S-March/smarchWand_Public/Firmware/ble_app_barebone_wand/src/config/user_config.h

/**
 ****************************************************************************************
 *
 * @file user_config.h
 *
 * @brief User configuration file.
 *
 * Copyright (C) 2015-2020 Dialog Semiconductor.
 * This computer program includes Confidential, Proprietary Information
 * of Dialog Semiconductor. All Rights Reserved.
 *
 ****************************************************************************************
 */

#ifndef _USER_CONFIG_H_
#define _USER_CONFIG_H_

/*
 * INCLUDE FILES
 ****************************************************************************************
 */

#include "app_user_config.h"
#include "arch_api.h"
#include "app_default_handlers.h"
#include "app_adv_data.h"
#include "co_bt.h"

/*
 * DEFINES
 ****************************************************************************************
 */

/*
 ****************************************************************************************
 *
 * Privacy / Addressing configuration
 *
 ****************************************************************************************
 */

/*************************************************************************
 * Privacy Capabilities and address configuration of local device:
 * - APP_CFG_ADDR_PUB               No Privacy, Public BDA
 * - APP_CFG_ADDR_STATIC            No Privacy, Random Static BDA
 * - APP_CFG_HOST_PRIV_RPA          Host Privacy, RPA, Public Identity
 * - APP_CFG_HOST_PRIV_NRPA         Host Privacy, NRPA (non-connectable ONLY)
 * - APP_CFG_CNTL_PRIV_RPA_PUB      Controller Privacy, RPA or PUB, Public Identity
 * - APP_CFG_CNTL_PRIV_RPA_RAND     Controller Privacy, RPA, Public Identity
 *
 * Select only one option for privacy / addressing configuration.
 **************************************************************************
 */
#define USER_CFG_ADDRESS_MODE       APP_CFG_ADDR_PUB

/*************************************************************************
 * Controller Privacy Mode:
 * - APP_CFG_CNTL_PRIV_MODE_NETWORK Controler Privacy Network mode (default)
 * - APP_CFG_CNTL_PRIV_MODE_DEVICE  Controler Privacy Device mode
 *
 * Select only one option for controller privacy mode configuration.
 **************************************************************************
 */
#define USER_CFG_CNTL_PRIV_MODE     APP_CFG_CNTL_PRIV_MODE_NETWORK

/*
 * VARIABLES
 ****************************************************************************************
 */

/******************************************
 * Default sleep mode. Possible values are:
 *
 * - ARCH_SLEEP_OFF
 * - ARCH_EXT_SLEEP_ON
 * - ARCH_EXT_SLEEP_OTP_COPY_ON
 *
 ******************************************
 */
static const sleep_state_t app_default_sleep_mode = ARCH_SLEEP_OFF;

/*
 ****************************************************************************************
 *
 * Advertising configuration
 *
 ****************************************************************************************
 */
static const struct advertise_configuration user_adv_conf = {

    .addr_src = APP_CFG_ADDR_SRC(USER_CFG_ADDRESS_MODE),

    /// Minimum interval for advertising
    .intv_min = MS_TO_BLESLOTS(687.5),                    // 687.5ms

    /// Maximum interval for advertising
    .intv_max = MS_TO_BLESLOTS(687.5),                    // 687.5ms

    /**
     *  Advertising channels map:
     * - ADV_CHNL_37_EN:   Advertising channel map for channel 37.
     * - ADV_CHNL_38_EN:   Advertising channel map for channel 38.
     * - ADV_CHNL_39_EN:   Advertising channel map for channel 39.
     * - ADV_ALL_CHNLS_EN: Advertising channel map for channel 37, 38 and 39.
     */
    .channel_map = ADV_ALL_CHNLS_EN,

    /*************************
     * Advertising information
     *************************
     */

    /// Host information advertising data (GAPM_ADV_NON_CONN and GAPM_ADV_UNDIRECT)
    /// Advertising mode :
    /// - GAP_NON_DISCOVERABLE: Non discoverable mode
    /// - GAP_GEN_DISCOVERABLE: General discoverable mode
    /// - GAP_LIM_DISCOVERABLE: Limited discoverable mode
    /// - GAP_BROADCASTER_MODE: Broadcaster mode
    .mode = GAP_GEN_DISCOVERABLE,

    /// Host information advertising data (GAPM_ADV_NON_CONN and GAPM_ADV_UNDIRECT)
    /// Advertising filter policy:
    /// - ADV_ALLOW_SCAN_ANY_CON_ANY: Allow both scan and connection requests from anyone
    /// - ADV_ALLOW_SCAN_ANY_CON_WLST: Allow both scan req from anyone and connection req from
    ///                                White List devices only
    .adv_filt_policy = ADV_ALLOW_SCAN_ANY_CON_ANY,

    /// Address of peer device
    /// NOTE: Meant for directed advertising (ADV_DIRECT_IND)
    .peer_addr = {0x1, 0x2, 0x3, 0x4, 0x5, 0x6},

    /// Address type of peer device (0=public/1=random)
    /// NOTE: Meant for directed advertising (ADV_DIRECT_IND)
    .peer_addr_type = 0,
};

/*
 ****************************************************************************************
 *
 * Advertising or scan response data for the following cases:
 *
 * - ADV_IND: Connectable undirected advertising event.
 *    - The maximum length of the user defined advertising data shall be 28 bytes.
 *    - The Flags data type are written by the related ROM function, hence the user shall
 *      not include them in the advertising data. The related ROM function adds 3 bytes in
 *      the start of the advertising data that are to be transmitted over the air.
 *    - The maximum length of the user defined response data shall be 31 bytes.
 *
 * - ADV_NONCONN_IND: Non-connectable undirected advertising event.
 *    - The maximum length of the user defined advertising data shall be 31 bytes.
 *    - The Flags data type may be omitted, hence the user can use all the 31 bytes for
 *      data.
 *    - The scan response data shall be empty.
 *
 * - ADV_SCAN_IND: Scannable undirected advertising event.
 *    - The maximum length of the user defined advertising data shall be 31 bytes.
 *    - The Flags data type may be omitted, hence the user can use all the 31 bytes for
 *      data.
 *    - The maximum length of the user defined response data shall be 31 bytes.
 ****************************************************************************************
 */
/// Advertising data
#define USER_ADVERTISE_DATA         "\x03"\
                                    ADV_TYPE_COMPLETE_LIST_16BIT_SERVICE_IDS\
                                    ADV_UUID_DEVICE_INFORMATION_SERVICE

/// Advertising data length - maximum 28 bytes, 3 bytes are reserved to set
#define USER_ADVERTISE_DATA_LEN               (sizeof(USER_ADVERTISE_DATA)-1)

/// Scan response data
#define USER_ADVERTISE_SCAN_RESPONSE_DATA ""

/// Scan response data length- maximum 31 bytes
#define USER_ADVERTISE_SCAN_RESPONSE_DATA_LEN (sizeof(USER_ADVERTISE_SCAN_RESPONSE_DATA)-1)

/*
 ****************************************************************************************
 *
 * Device name.
 *
 * - If there is space left in the advertising or scan response data the device name is
 *   copied there. The device name can be anytime read by a connected peer, if the
 *   application supports it.
 * - The Bluetooth device name can be up to 248 bytes.
 *
 ****************************************************************************************
 */
/// Device name
#define USER_DEVICE_NAME        "smarchHouse"

/// Device name length
#define USER_DEVICE_NAME_LEN    (sizeof(USER_DEVICE_NAME)-1)

/*
 ****************************************************************************************
 *
 * GAPM configuration
 *
 ****************************************************************************************
 */
static const struct gapm_configuration user_gapm_conf = {
    /// Device Role: Central, Peripheral, Observer, Broadcaster or All roles. (@see enum gap_role)
    .role = GAP_ROLE_PERIPHERAL,

    /// Maximal MTU. Shall be set to 23 if Legacy Pairing is used, 65 if Secure Connection is used,
    /// more if required by the application
    .max_mtu = 23,

    /// Device Address Type
    .addr_type = APP_CFG_ADDR_TYPE(USER_CFG_ADDRESS_MODE),
    /// Duration before regenerating the Random Private Address when privacy is enabled
    .renew_dur = 15000,    // 15000 * 10ms = 150s is the minimum value

    /***********************
     * Privacy configuration
     ***********************
     */

    /// Random Static address
    // NOTE: The address shall comply with the following requirements:
    // - the two most significant bits of the address shall be equal to 1,
    // - all the remaining bits of the address shall NOT be equal to 1,
    // - all the remaining bits of the address shall NOT be equal to 0.
    // In case the {0x00, 0x00, 0x00, 0x00, 0x00, 0x00} null address is used, a
    // random static address will be automatically generated.
    .addr = {0x00, 0x00, 0x00, 0x00, 0x00, 0x00},

    /// Device IRK used for Resolvable Private Address generation (LSB first)
    .irk = {0x00, 0x01, 0x02, 0x03, 0x04, 0x05, 0x06, 0x07, 0x08, 0x09, 0x0a, 0x0b, 0x0c, 0x0d, 0x0e, 0x0f},

    /****************************
     * ATT database configuration
     ****************************
     */

    /// Attribute database configuration (@see enum gapm_att_cfg_flag)
    ///    7     6    5     4     3    2    1    0
    /// +-----+-----+----+-----+-----+----+----+----+
    /// | DBG | RFU | SC | PCP | APP_PERM |NAME_PERM|
    /// +-----+-----+----+-----+-----+----+----+----+
    /// - Bit [0-1]: Device Name write permission requirements for peer device (@see device_name_write_perm)
    /// - Bit [2-3]: Device Appearance write permission requirements for peer device (@see device_appearance_write_perm)
    /// - Bit [4]  : Slave Preferred Connection Parameters present
    /// - Bit [5]  : Service change feature present in GATT attribute database.
    /// - Bit [6]  : Reserved
    /// - Bit [7]  : Enable Debug Mode
    .att_cfg = GAPM_MASK_ATT_SVC_CHG_EN,

    /// GAP service start handle
    .gap_start_hdl = 0,

    /// GATT service start handle
    .gatt_start_hdl = 0,

    /**************************************************
     * Data packet length extension configuration (4.2)
     **************************************************
     */

    /// Maximal MPS
    .max_mps = 0,

    /// Maximal Tx octets (connInitialMaxTxOctets value, as defined in 4.2 Specification)
    .max_txoctets = 251,

    /// Maximal Tx time (connInitialMaxTxTime value, as defined in 4.2 Specification)
    .max_txtime = 2120,
};

/*
 ****************************************************************************************
 *
 * Parameter update configuration
 *
 ****************************************************************************************
 */
static const struct connection_param_configuration user_connection_param_conf = {
    /// Connection interval minimum measured in ble double slots (1.25ms)
    /// use the macro MS_TO_DOUBLESLOTS to convert from milliseconds (ms) to double slots
    .intv_min = MS_TO_DOUBLESLOTS(10),

    /// Connection interval maximum measured in ble double slots (1.25ms)
    /// use the macro MS_TO_DOUBLESLOTS to convert from milliseconds (ms) to double slots
    .intv_max = MS_TO_DOUBLESLOTS(20),

    /// Latency measured in connection events
    .latency = 0,

    /// Supervision timeout measured in timer units (10 ms)
    /// use the macro MS_TO_TIMERUNITS to convert from milliseconds (ms) to timer units
    .time_out = MS_TO_TIMERUNITS(1250),

    /// Minimum Connection Event Duration measured in ble double slots (1.25ms)
    /// use the macro MS_TO_DOUBLESLOTS to convert from milliseconds (ms) to double slots
    .ce_len_min = MS_TO_DOUBLESLOTS(0),

    /// Maximum Connection Event Duration measured in ble double slots (1.25ms)
    /// use the macro MS_TO_DOUBLESLOTS to convert from milliseconds (ms) to double slots
    .ce_len_max = MS_TO_DOUBLESLOTS(0),
};

/*
 ****************************************************************************************
 *
 * Default handlers configuration (applies only for @app_default_handlers.c)
 *
 ****************************************************************************************
 */
static const struct default_handlers_configuration  user_default_hnd_conf = {
    // Configure the advertise operation used by the default handlers
    // Possible values:
    //  - DEF_ADV_FOREVER
    //  - DEF_ADV_WITH_TIMEOUT
    .adv_scenario = DEF_ADV_FOREVER,

    // Configure the advertise period in case of DEF_ADV_WITH_TIMEOUT.
    // It is measured in timer units (3 min). Use MS_TO_TIMERUNITS macro to convert
    // from milliseconds (ms) to timer units.
    .advertise_period = MS_TO_TIMERUNITS(180000),

    // Configure the security start operation of the default handlers
    // if the security is enabled (CFG_APP_SECURITY)
    // Possible values:
    //  - DEF_SEC_REQ_NEVER
    //  - DEF_SEC_REQ_ON_CONNECT
    .security_request_scenario = DEF_SEC_REQ_NEVER
};

/*
 ****************************************************************************************
 *
 * Central configuration (not used by current example)
 *
 ****************************************************************************************
 */
static const struct central_configuration user_central_conf = {
    /// GAPM requested operation:
    /// - GAPM_CONNECTION_DIRECT: Direct connection operation
    /// - GAPM_CONNECTION_AUTO: Automatic connection operation
    /// - GAPM_CONNECTION_SELECTIVE: Selective connection operation
    /// - GAPM_CONNECTION_NAME_REQUEST: Name Request operation (requires to start a direct
    ///   connection)
    .code = GAPM_CONNECTION_DIRECT,

    /// Own BD address source of the device:
    .addr_src = APP_CFG_ADDR_SRC(USER_CFG_ADDRESS_MODE),

    /// Scan interval
    .scan_interval = 0x180,

    /// Scan window size
    .scan_window = 0x160,

     /// Minimum of connection interval
    .con_intv_min = 100,

    /// Maximum of connection interval
    .con_intv_max = 100,

    /// Connection latency
    .con_latency = 0,

    /// Link supervision timeout
    .superv_to = 0x1F4,

     /// Minimum CE length
    .ce_len_min = 0,

    /// Maximum CE length
    .ce_len_max = 0x5,

    /**************************************************************************************
     * Peer device information (maximum number of peers = 8)
     **************************************************************************************
     */

    /// BD Address of device
    .peer_addr_0 = {0x0, 0x0, 0x0, 0x0, 0x0, 0x0},

    /// Address type of the device 0=public/1=random
    .peer_addr_0_type = 0,

    /// BD Address of device
    .peer_addr_1 = {0x0, 0x0, 0x0, 0x0, 0x0, 0x0},

    /// Address type of the device 0=public/1=random
    .peer_addr_1_type = 0,

    /// BD Address of device
    .peer_addr_2 = {0x0, 0x0, 0x0, 0x0, 0x0, 0x0},

    /// Address type of the device 0=public/1=random
    .peer_addr_2_type = 0,

    /// BD Address of device
    .peer_addr_3 = {0x0, 0x0, 0x0, 0x0, 0x0, 0x0},

    /// Address type of the device 0=public/1=random
    .peer_addr_3_type = 0,

    /// BD Address of device
    .peer_addr_4 = {0x0, 0x0, 0x0, 0x0, 0x0, 0x0},

    /// Address type of the device 0=public/1=random
    .peer_addr_4_type = 0,

    /// BD Address of device
    .peer_addr_5 = {0x0, 0x0, 0x0, 0x0, 0x0, 0x0},

    /// Address type of the device 0=public/1=random
    .peer_addr_5_type = 0,

    /// BD Address of device
    .peer_addr_6 = {0x0, 0x0, 0x0, 0x0, 0x0, 0x0},

    /// Address type of the device 0=public/1=random
    .peer_addr_6_type = 0,

    /// BD Address of device
    .peer_addr_7 = {0x0, 0x0, 0x0, 0x0, 0x0, 0x0},

    /// Address type of the device 0=public/1=random
    .peer_addr_7_type = 0,
};

/*
 ****************************************************************************************
 *
 * Security related configuration
 *
 ****************************************************************************************
 */
static const struct security_configuration user_security_conf = {
    // IO Capabilities
    #if defined (USER_CFG_FEAT_IO_CAP)
    .iocap          = USER_CFG_FEAT_IO_CAP,
    #else
    .iocap          = GAP_IO_CAP_NO_INPUT_NO_OUTPUT,
    #endif

    // OOB Capabilities
    #if defined (USER_CFG_FEAT_OOB)
    .oob            = USER_CFG_FEAT_OOB,
    #else
    .oob            = GAP_OOB_AUTH_DATA_NOT_PRESENT,
    #endif

    // Authentication Requirements
    #if defined (USER_CFG_FEAT_AUTH_REQ)
    .auth           = USER_CFG_FEAT_AUTH_REQ,
    #else
    .auth           = GAP_AUTH_NONE,
    #endif

    // LTK size
    #if defined (USER_CFG_FEAT_KEY_SIZE)
    .key_size       = USER_CFG_FEAT_KEY_SIZE,
    #else
    .key_size       = KEY_LEN,
    #endif

    // Initiator key distribution
    #if defined (USER_CFG_FEAT_INIT_KDIST)
    .ikey_dist      = USER_CFG_FEAT_INIT_KDIST,
    #else
    .ikey_dist      = GAP_KDIST_NONE,
    #endif

    // Responder key distribution
    #if defined (USER_CFG_FEAT_RESP_KDIST)
    .rkey_dist      = USER_CFG_FEAT_RESP_KDIST,
    #else
    .rkey_dist      = GAP_KDIST_ENCKEY,
    #endif

    // Security requirements (minimum security level)
    #if defined (USER_CFG_FEAT_SEC_REQ)
    .sec_req        = USER_CFG_FEAT_SEC_REQ,
    #else
    .sec_req        = GAP_NO_SEC,
    #endif
};

#endif // _USER_CONFIG_H_
