S-March/smarchWand_Public/Firmware/ble_app_barebone_wand/src/user_wakeup.c

/**
 ****************************************************************************************
 *
 * @file user_wakeup.c
 *
 * @brief uder wakeup source code.
 *
 * Copyright (c) 2015-2019 Dialog Semiconductor. All rights reserved.
 *
 * This software ("Software") is owned by Dialog Semiconductor.
 *
 * By using this Software you agree that Dialog Semiconductor retains all
 * intellectual property and proprietary rights in and to this Software and any
 * use, reproduction, disclosure or distribution of the Software without express
 * written permission or a license agreement from Dialog Semiconductor is
 * strictly prohibited. This Software is solely for use on or in conjunction
 * with Dialog Semiconductor products.
 *
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
 ****************************************************************************************
 */

/**
 ****************************************************************************************
 * @addtogroup APP
 * @{
 ****************************************************************************************
 */

/*
 * INCLUDE FILES
 ****************************************************************************************
 */
#include "wkupct_quadec.h" 
#include "user_wakeup.h"
#include "user_periph_setup.h"
#include "uart_utils.h"
#include "user_barebone.h"
#include "arch_console.h"

/*
 * TYPE DEFINITIONS
 ****************************************************************************************
 */


/*
 * GLOBAL VARIABLE DEFINITIONS
 ****************************************************************************************
 */


/*
 * FUNCTION DEFINITIONS
 ****************************************************************************************
*/

#if defined(__DA14531__)
/**
 ****************************************************************************************
 * @brief reset function for the event counter of the DA14531
 * @return void
 ****************************************************************************************
 */
void user_reset_event_counter(void){

   SetWord16(WKUP_IRQ_STATUS_REG, WKUP_CNTR_RST);

}
#endif

/**
 ****************************************************************************************
 * @brief Button press callback function. Registered in WKUPCT driver.
 * @return void
 ****************************************************************************************
 */
void user_app_wakeup_press_cb(void)
{
	SetBits16(WKUP_CTRL_REG, WKUP_ENABLE_IRQ, INTERRUPT_ENABLE); //Resets interupt
	if (arch_ble_ext_wakeup_get())
	{
		arch_set_sleep_mode(ARCH_SLEEP_OFF);
		arch_ble_force_wakeup();
		arch_ble_ext_wakeup_off();
		// If wakeup is generated by SW2
		if(!GPIO_GetPinStatus(GPIO_BUTTON_PORT, GPIO_BUTTON_PIN))						
		{										
				#ifdef CFG_PRINTF_UART2
				arch_printf("\n\n\rWakeup source: INT\n\n\r",NULL);
				user_app_waking_from_sleep();
				#endif
		}
		// If state is idle, start advertising
		if (ke_state_get(TASK_APP) == APP_CONNECTABLE)
		{
				user_app_adv_start();
		}
		
	}
//	else if (!arch_ble_ext_wakeup_get()){
//		#ifdef CFG_PRINTF_UART2
//				arch_printf("\n\n\rSystem going to sleep",NULL);
//							
//		#endif
//		GPIO_SetInactive(LED_PORT, LED_PIN);
//			user_app_going_to_sleep();

////		#ifdef SLEEP_WITHOUT_ADVERTISING
//				app_easy_gap_advertise_stop();
////		#endif

//		arch_set_sleep_mode(ARCH_EXT_SLEEP_ON);				
//		arch_ble_ext_wakeup_on();
//		
//	}                                                               
	#if defined(__DA14531__)
		user_reset_event_counter(); // When callback is triggerd the event counter is not set 0 for the 531, that is why this function is called. 
	#endif								 	 			// For the 585 the event counter is set to 0 even before reaching this (user_app_wakeup_press_cb) callback funtion.
												  	
}


/**
 ****************************************************************************************
 * @brief Sets sw2 and sw3 as wake up trigger
 * @return void
 ****************************************************************************************
*/
void user_wakeup_example_init(void)
{
		wkupct_enable_irq((WKUPCT_PIN_SELECT(GPIO_BUTTON_PORT, GPIO_BUTTON_PIN)), 						// When enabling more than one interruptsource use OR bitoperation. WKUPCT_PIN_SELECT will make sure the appropriate bit in the register is set. 
											(WKUPCT_PIN_POLARITY(GPIO_BUTTON_PORT, GPIO_BUTTON_PIN, WKUPCT_PIN_POLARITY_LOW)),	// When enabling more than one interruptsource use OR bitoperation. WKUPCT_PIN_POLARITY will make sure the appriopriate bit in the register is set.
											EVENTS_BEFORE_INTERRUPT,																																																													
											DEBOUNCE_TIME);																																																												
	
		wkupct_register_callback(user_app_wakeup_press_cb);	// sets this function as wake-up interrupt callback
}

/// @} APP
